betamoojw/hdmi-ddc-input-switch/web/images/step1-tray-inserts.png

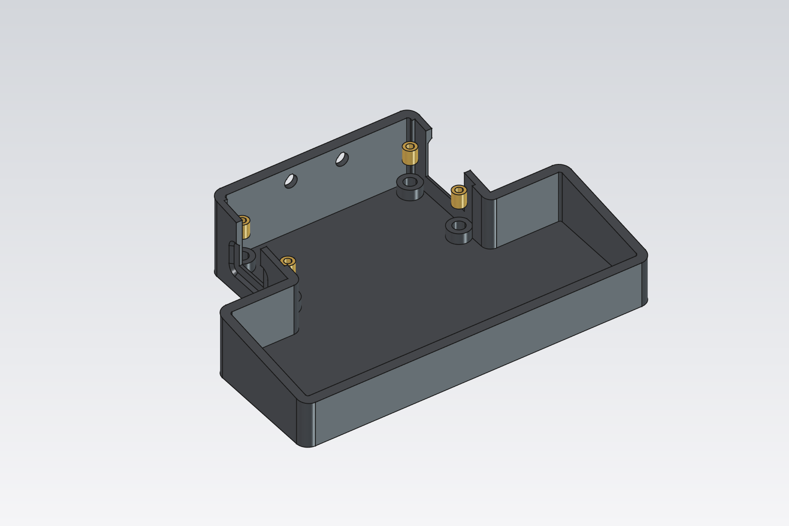
web/images/step1-tray-inserts.png
