betamoojw/hdmi-ddc-input-switch/web/images/step4-plate-buttons.png

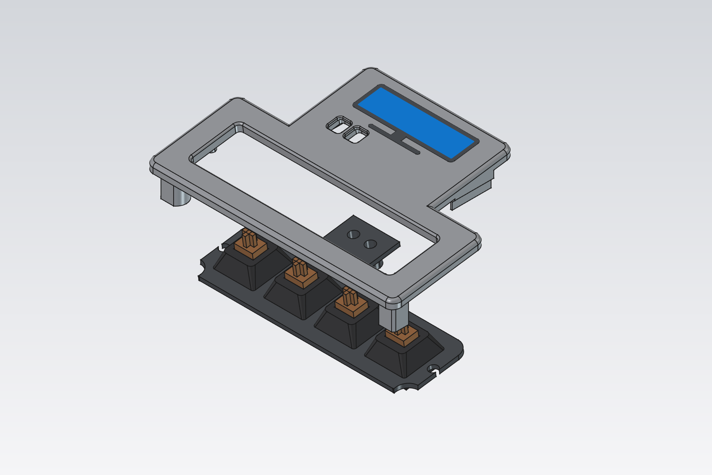
web/images/step4-plate-buttons.png
